poetaster/moat/CAD/monsters.png

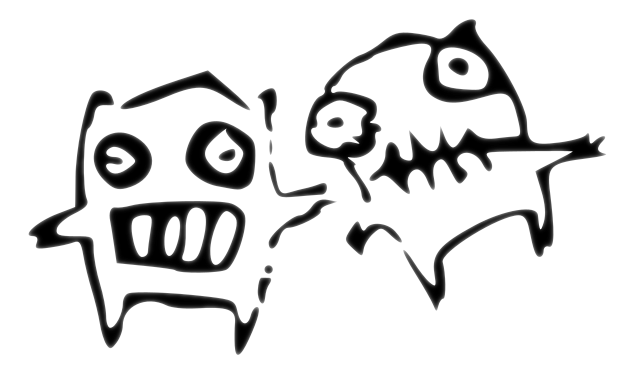
CAD/monsters.png
