poetaster/moat/doc/12-keep-intro.jpg

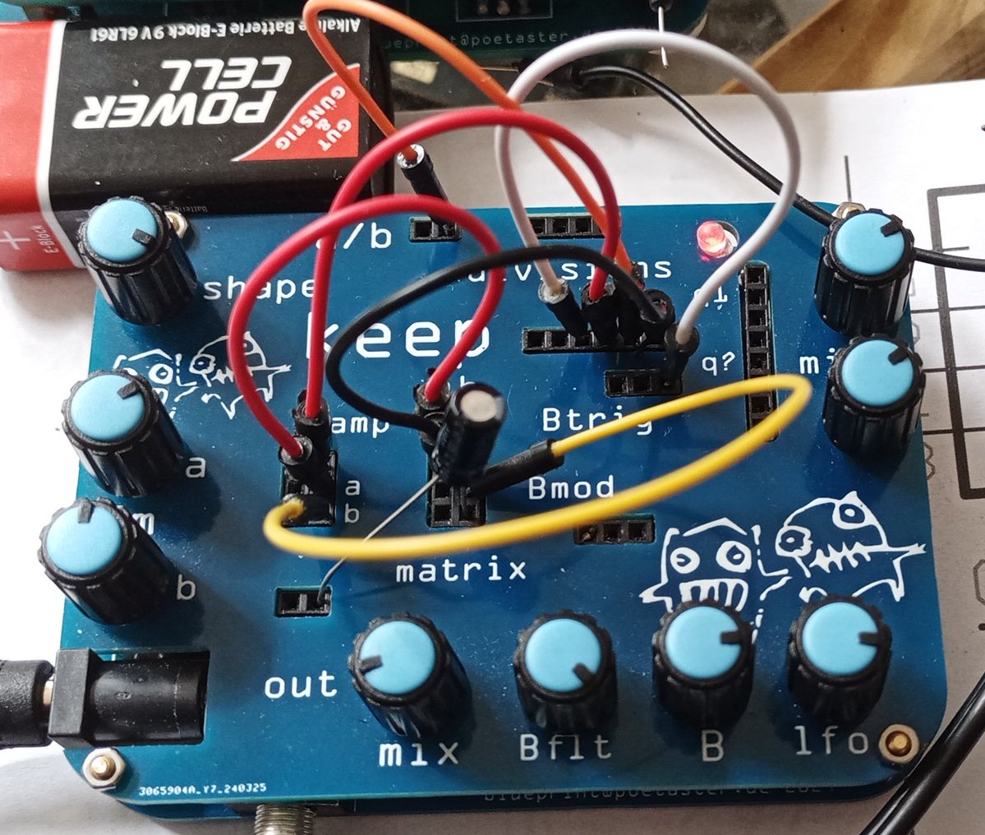
doc/12-keep-intro.jpg
