poetaster/moat/historical/keep.v3_pcb.jpg

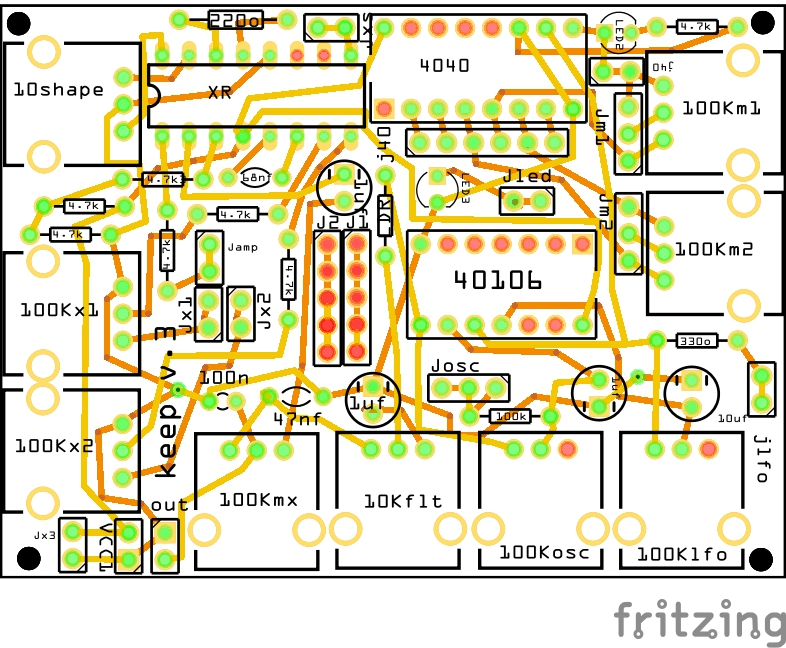
historical/keep.v3_pcb.jpg
