poetaster/moat/historical/moat.v2_pcb.png

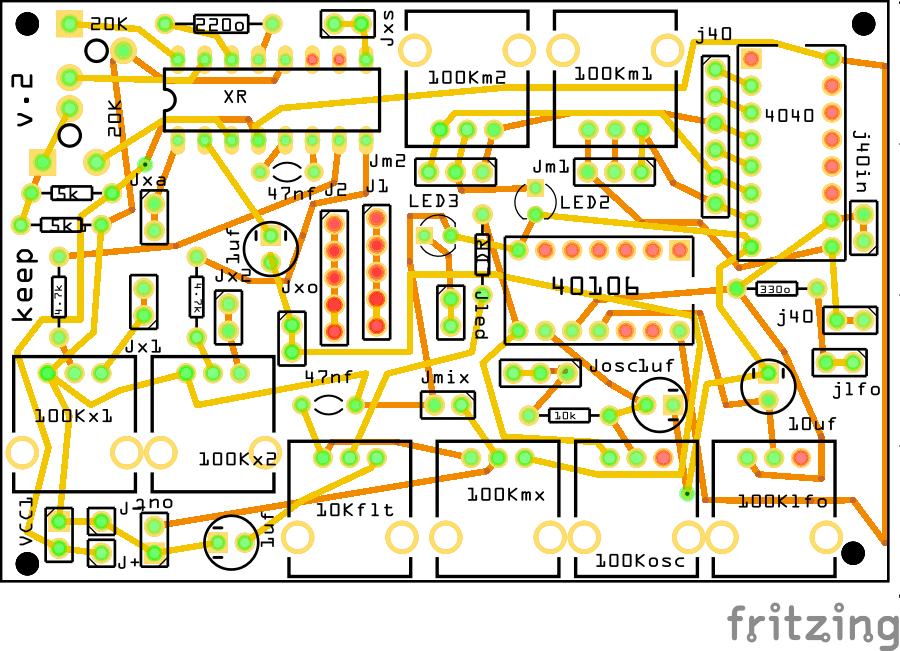
historical/moat.v2_pcb.png
